OSHE-Github/Plant-Saver/Plant_Saver_Spring_2026/Code/Plant_Saver_Spring_2026/PlantSaverAssets.h

#ifndef PlantSaverAssets_h
#define PlantSaverAssets_h

// 16x8
static const unsigned char PROGMEM upArrowBmp[] = 
{ 0b00000001, 0b10000000,
  0b00000011, 0b11000000,
  0b00000011, 0b11000000,
  0b00000111, 0b11100000,
  0b00000111, 0b11100000,
  0b00001111, 0b11110000,
  0b00001111, 0b11110000,
  0b00011111, 0b11111000 };

// 16x8
static const unsigned char PROGMEM downArrowBmp[] = 
{ 0b00011111, 0b11111000,
  0b00001111, 0b11110000,
  0b00001111, 0b11110000,
  0b00000111, 0b11100000,
  0b00000111, 0b11100000,
  0b00000011, 0b11000000,
  0b00000011, 0b11000000,
  0b00000001, 0b10000000 };

// 11x11
static const unsigned char PROGMEM lightBmp[] = 
{ 0b00000100, 0b00000000,
  0b01000100, 0b01000000,
  0b00100000, 0b10000000,
  0b00001110, 0b00000000,
  0b00010001, 0b00000000,
  0b11010001, 0b01100000,
  0b00010001, 0b00000000,
  0b00001110, 0b00000000,
  0b00100000, 0b10000000,
  0b01000100, 0b01000000,
  0b00000100, 0b00000000 };

// 7x13
static const unsigned char PROGMEM waterBmp[] = 
{ 0b00010000,
  0b00010000,
  0b00101000,
  0b00101000,
  0b01000100,
  0b01000100,
  0b01000100,
  0b10000010,
  0b10000010,
  0b10000010,
  0b10000010,
  0b01000100,
  0b00111000 };

// 8x13
static const unsigned char PROGMEM tempBmp[] = 
{ 0b00011000,
  0b00100111,
  0b00100100,
  0b00100111,
  0b00100100,
  0b00100111,
  0b00100100,
  0b01000010,
  0b10000001,
  0b10000001,
  0b10000001,
  0b01000010,
  0b00111100 };

// 8x8
static const unsigned char PROGMEM degFBmp[] = 
{ 0b11100000,
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
 0b00000001, 0b11001110, 0b00000000,
 0b00000000, 0b01010010, 0b00000000,
 0b00000000, 0b00111100, 0b00000000,
 0b00000000, 0b00100000, 0b00000000,
 0b00000000, 0b00100000, 0b00000000,
 0b00000000, 0b00100000, 0b00000000,
 0b00000000, 0b00100000, 0b00000000 };

#endif
