OSHE-Github/Plant-Saver/Plant_Saver_Fall_2025/Plant_Saver_Fall_2025/PlantSaverClasses.h

#include "esp32-hal-rmt.h"
#ifndef PlantSaverClasses_h
#define PlantSaverClasses_h

#include <Arduino.h>
#include <ArduinoJson.h>
#include <Adafruit_GFX.h>
#include <Adafruit_SSD1306.h>

/*------------------------------------------------------------ Macros ------------------------------------------------------------*/

#define ERROR_IND_PIN 4  // Error indication LED

#define NUM_MENUS 3
#define SCREEN_WIDTH 128  // OLED display width, in pixels
#define SCREEN_HEIGHT 64  // OLED display height, in pixels
#define OLED_RESET -1     // OLED Reset pin # (or -1 if sharing Arduino reset pin)
#define NUM_DISPLAY_PLANTS 10
#define MAX_CHARS_FILENAME 21
#define NUM_CHARS_TIMESTAMP 25
#define MAX_SENSOR_READINGS 200  // # of sensor readings allowed in FIFO
#define NUM_CHARS_NAME 50
#define NUM_CHARS_FACT 100
#define NUM_DB_FILES 2

/*------------------------------------------------------- Class Definitions -------------------------------------------------------*/

// Data of plants pulled from the database
class DBPlant {
public:
  DBPlant();
  int id;  // ID within the plant database
  char commonName[NUM_CHARS_NAME];
  int hardiness[2];
  int lightReq[2];
  int waterReq[2];
  char scientificName[NUM_CHARS_NAME];
  char fact[NUM_CHARS_FACT];
};

// Data of plants actively being monitored
class Plant {
public:
  Plant();
  float getAvgReading(JsonDocument sensorDoc);
  void checkThresholds();
  int selfID;  // User Plant DB ID (1-5)
  int baseID;  // ID within the larger plant database
  char commonName[NUM_CHARS_NAME];
  char scientificName[NUM_CHARS_NAME];
  char fact[NUM_CHARS_FACT];
  int lightReq[2];
  int waterReq[2];
  int hardiness[2];
  float avgLight;
  float avgWater;
  float avgHumidity;
  float avgTemp;
  // These variables ARE NOT stored:
  int lightEval;
  int waterEval;
  int humidityEval;
  int tempEval;
private:
  void tempCheck();
  void waterCheck();
  void lightCheck();
  void humidityCheck();
};

// Data associated with an instanced multi-sensor reading
class SensorReading {
public:
  SensorReading();
  float tempReading;
  float waterReading;
  float humidityReading;
  float lightReading;
  int plantID;  // Self ID of the associated user plant - might be able to remove this since all are associated with a datagroup
  char timeStamp[NUM_CHARS_TIMESTAMP];
};

// Class for storing/retrieving header file data
class Header {
public:
  Header();
  int activePlantID;
  char date[NUM_CHARS_TIMESTAMP];
  int numDBPlants;  // Number of plants in the larger read-only database
  int lightThreshold;
  int tempThreshold;
  int waterThreshold;
  int humidityThreshold;
};

// Class to store/manipulate/report system errors
class Error {
public:
  Error();
  int getError(int errorStatus);
  void clearError(int errorStatus);
  void addError(int errorStatus);
  void indicateError();
  int highestPriority;
private:
  int _errorList[8];
  int _flashCt;
  int _flashDuration;
  bool _indicatorOn;
  unsigned long _startTime;
};

// Class to store data/methods surrounding the user interface
class Interface {
public:
  Interface();
  bool begin(uint8_t vcs, uint8_t addr);
  char getEvalIndicator(int eval);
  void displayMainMenu(Plant activePlant);
  void displayInfoMenu(Plant activePlant);
  void displaySelectMenu(char plantName[]);
  void nextScreen(Plant activePlant, char plantName[]);
  void displayOff();
  int selectedPlantIndex;
  int activeMenu;
};

// Class to store/pass around multiple objects between functions
class Container {
public:
  Container();
  void updatePlantData();
  void pullHeader();
  void pushHeader();
  void pullPlant();
  void pushPlant();
  void getDBPlants();
  void newUserPlant(int newSelfID);
  void addTimeStamp();
  void clearSensorData();
  Plant activePlant;
  Error error;
  Header header;
  SensorReading sensorReading;
  Interface interface;
  DBPlant plants[NUM_DISPLAY_PLANTS];
  int activeMode;
  bool plantPulled;
  bool dbPlantsPulled;
  bool headerPulled;
private:
  JsonDocument addSensorReading(JsonDocument sensorDoc, float reading);
};

/*------------------------------------------------------- Standalone Helpers -------------------------------------------------------*/

// Standalone file reader
JsonDocument readSDFile(char fileName[]);

// Standalone file writer
int pushJsonDoc(JsonDocument doc, char fileName[]);

// Standalone time utility
void getTimeStr(char* buffer);

// Standalone timekeeping utility
bool setTimeFromTimeStr(char timeStr[]);

/*---------------------------------------------------------- enumerables -----------------------------------------------------------*/

// For tracking states
enum StateTracker {
  startupMode,
  displayMode,
  sensingMode,
  triggerMode,
  shutdownMode,
  errorMode
};

// For tracking current menu
enum Menu {
  noMenu,
  mainMenu,
  infoMenu,
  selectMenu,
  triggerMenu
};

// For returning/parsing error status from functions
enum ErrorStatus {
  noError,
  displayInit,
  lightSensorInit,
  tempSensorInit,
  moistureSensorInit,
  jsonError,
  fileOperation,
  SDInit
};

// For iterating through multiple files
enum FileTypes {
  lightFile,
  waterFile,
  humidityFile,
  tempFile,
  datesFile
};

// For iterating/checking threshold evaluations
enum Eval {
  evalUnknown,
  evalLow,
  evalHigh,
  evalOK
};

// For checking light requirements
enum LightValues {
  fullShade = 1,
  partialSun = 2,
  fullSun = 3
};

// For checking water requirements
enum waterValues {
  water = 1,
  wet = 2,
  moist = 3,
  dry = 4
};

#endif
